Gixy31/ESP32-PoolMaster/Nextion/HMI_BlueTheme/ressources/HMI2_Calibs.png

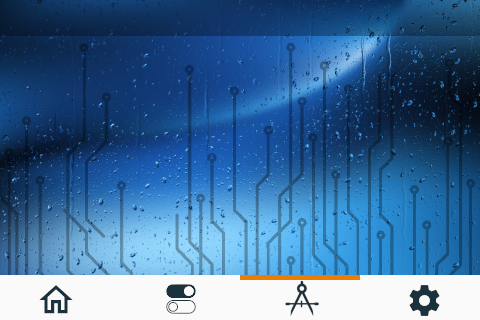
Nextion/HMI_BlueTheme/ressources/HMI2_Calibs.png
