Gixy31/ESP32-PoolMaster/Nextion/HMI_BlueTheme/ressources/HMI2_Home.png

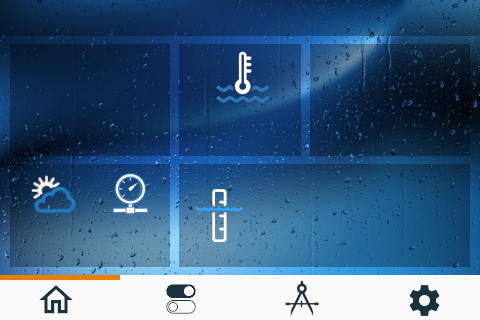
Nextion/HMI_BlueTheme/ressources/HMI2_Home.png
