Gixy31/ESP32-PoolMaster/pH_Orp Board V2/Bottom.jpg

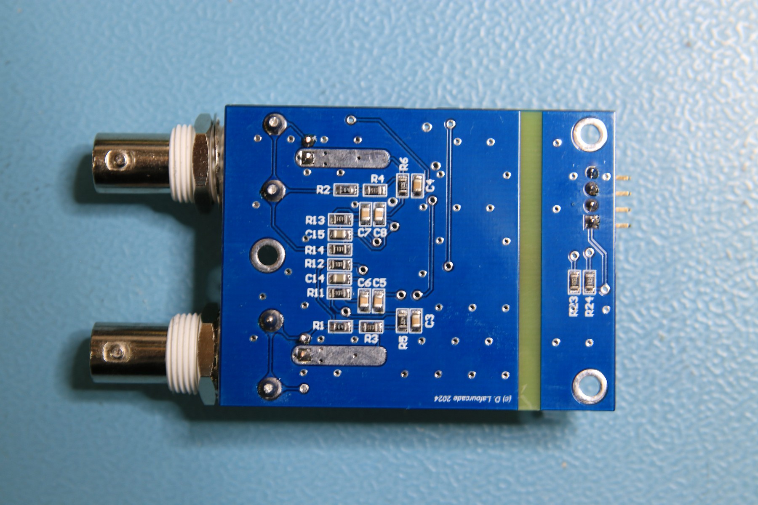
pH_Orp Board V2/Bottom.jpg
