Gixy31/ESP32-PoolMaster/pH_Orp Board V2/Top.jpg

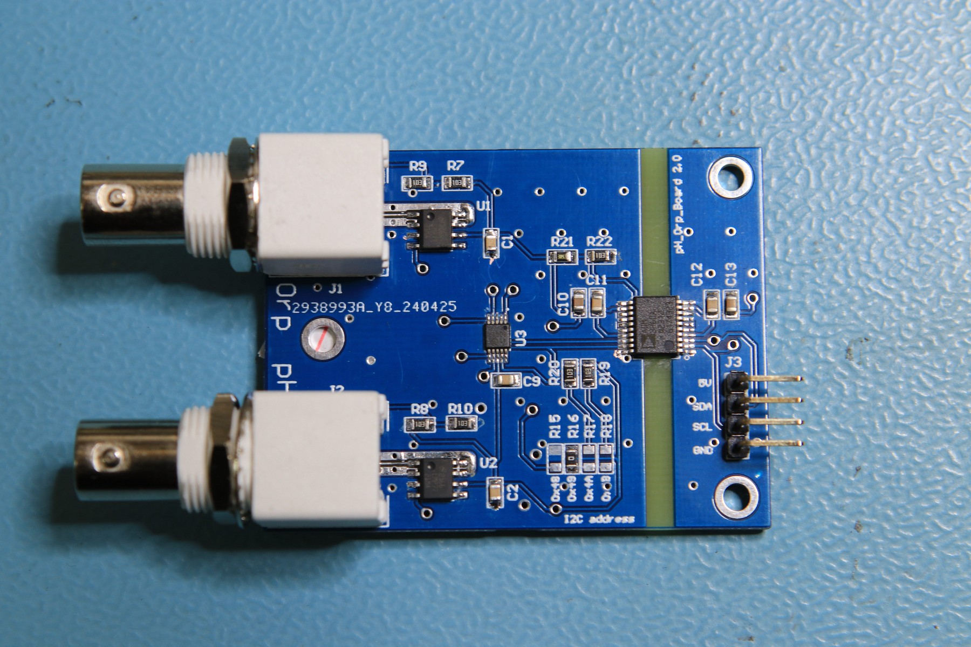
pH_Orp Board V2/Top.jpg
